JensenK17/ioT_putting_analysis/docs/final_training_confusion_matrix.png

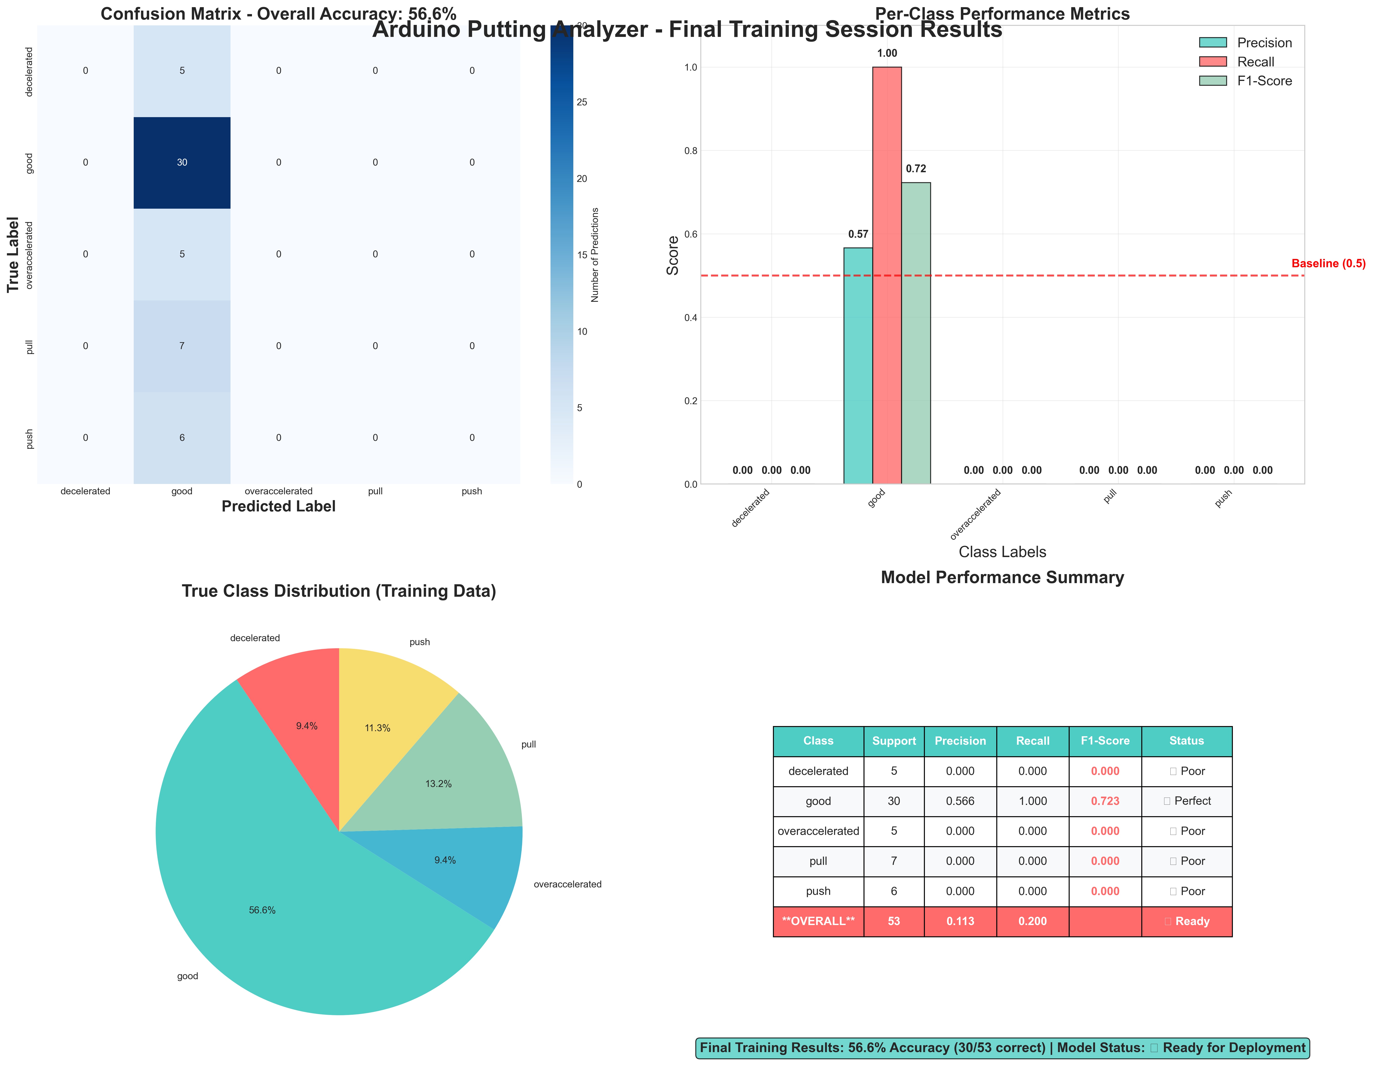
docs/final_training_confusion_matrix.png
