JensenK17/ioT_putting_analysis/docs/model_insights_recommendations.png

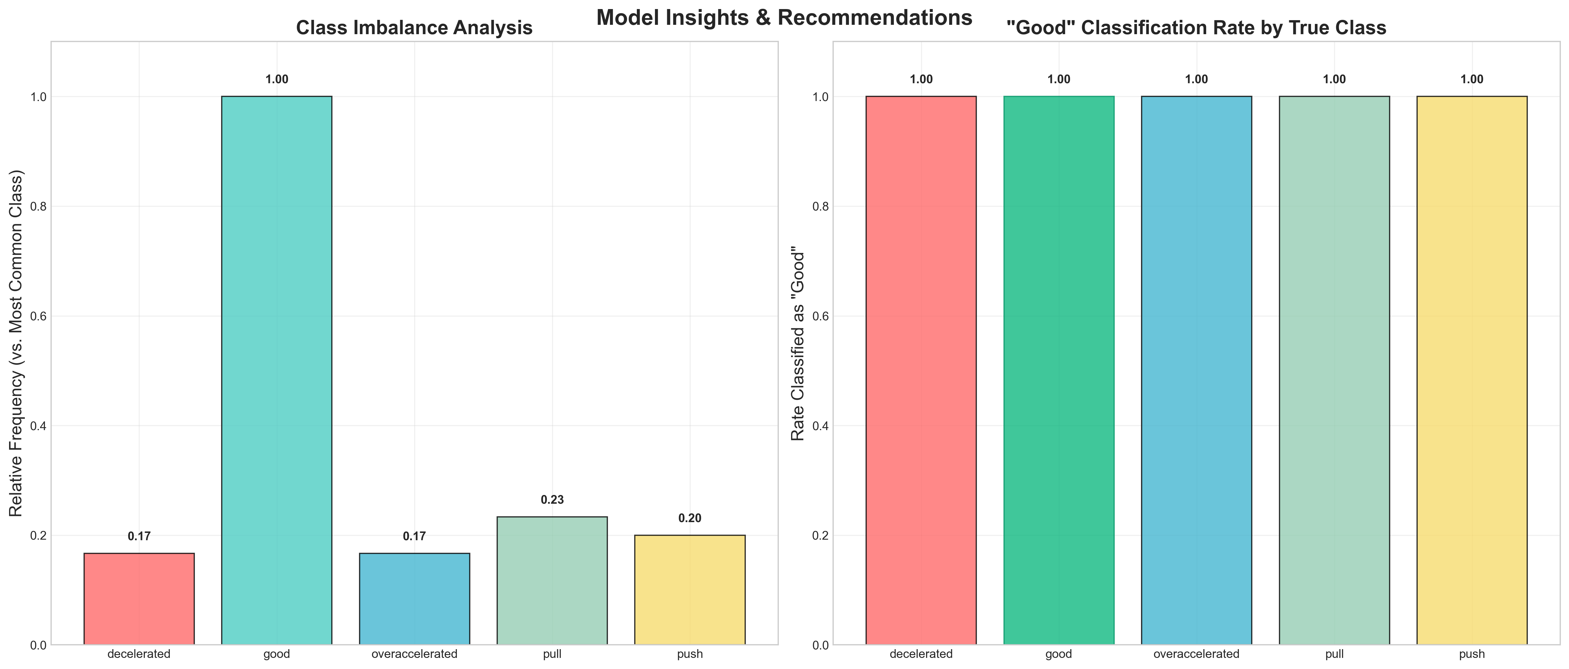
docs/model_insights_recommendations.png
