JensenK17/ioT_putting_analysis/Putting_Device/SS_of_putting_analysis_pcb_V0.png

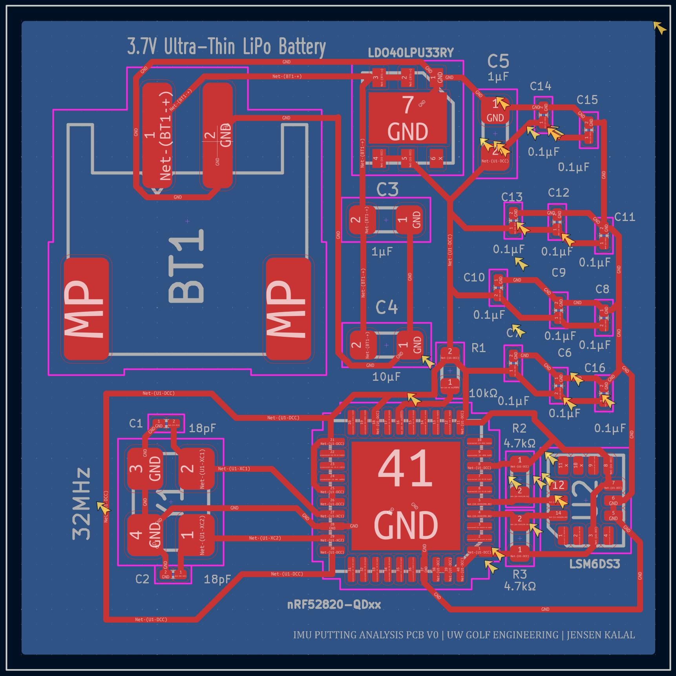
Putting_Device/SS_of_putting_analysis_pcb_V0.png
