JensenK17/ioT_putting_analysis/docs/detailed_performance_analysis.png

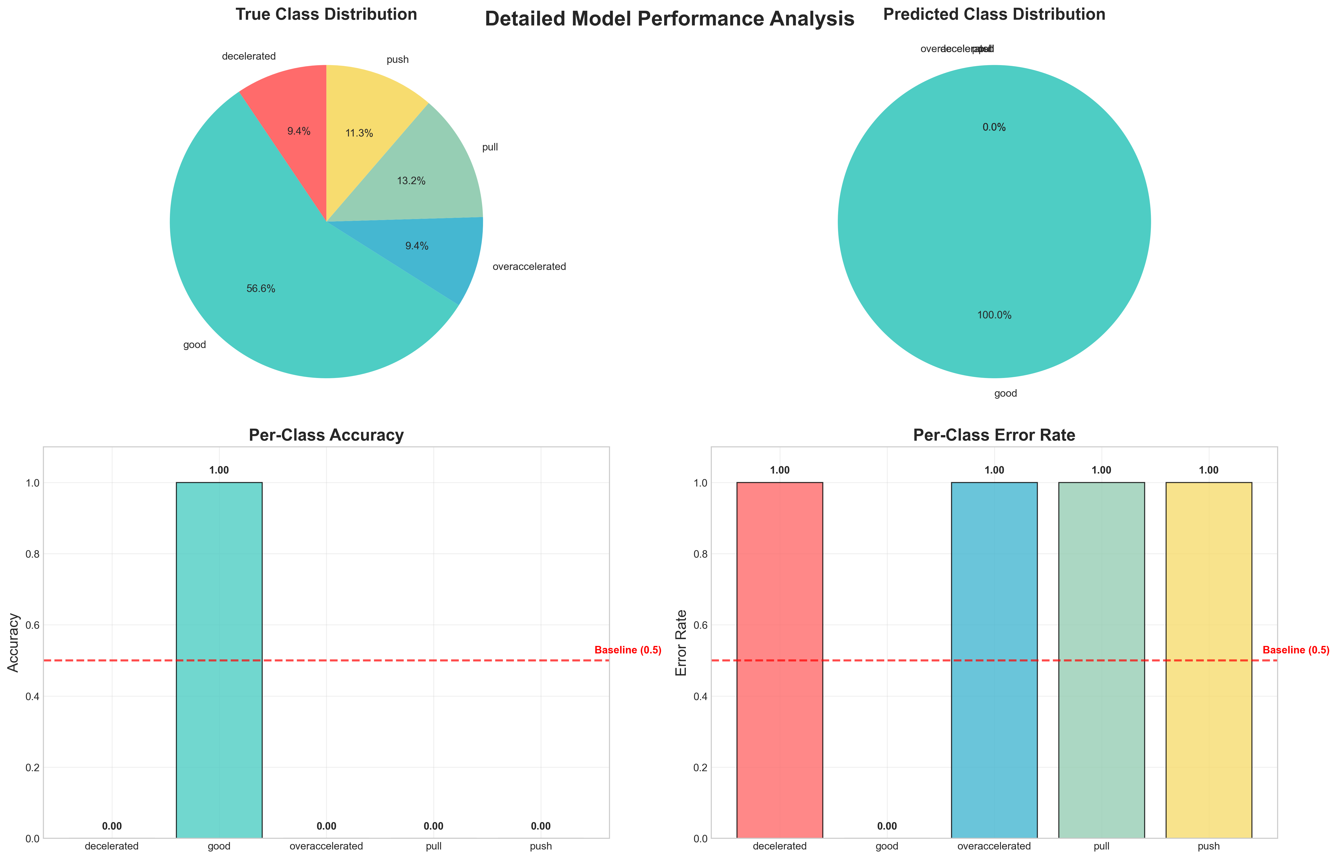
docs/detailed_performance_analysis.png
