JensenK17/ioT_putting_analysis/docs/performance_summary_table.png

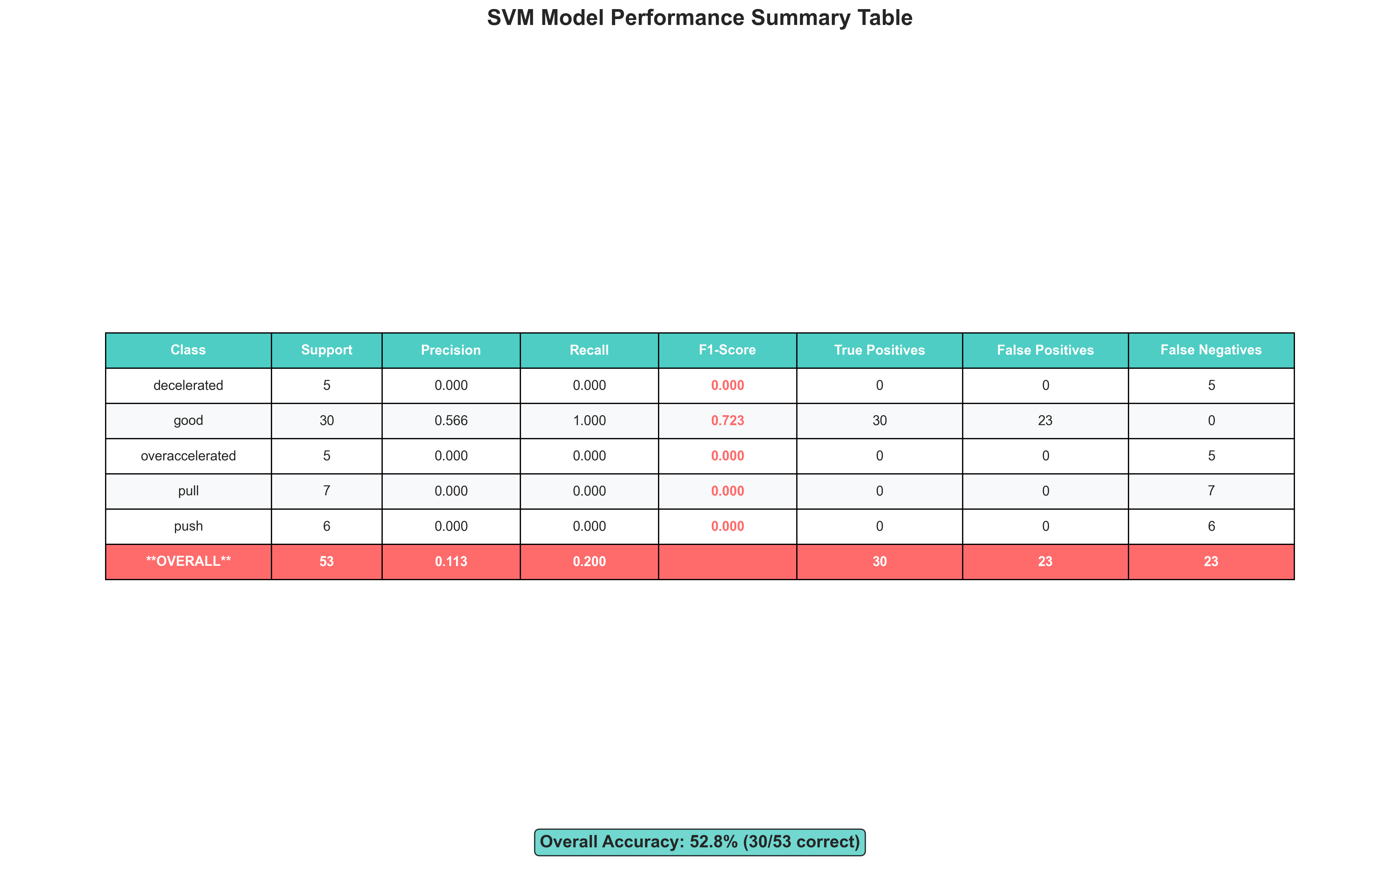
docs/performance_summary_table.png
